SirSerow/ESP-32_Smart_Button/doc/battery_view.jpg

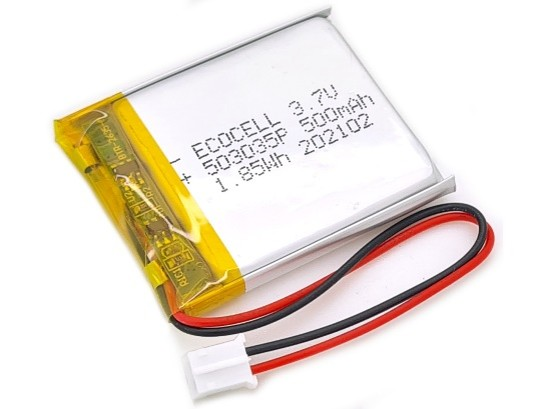
doc/battery_view.jpg
