SirSerow/ESP-32_Smart_Button/doc/cad_view.png

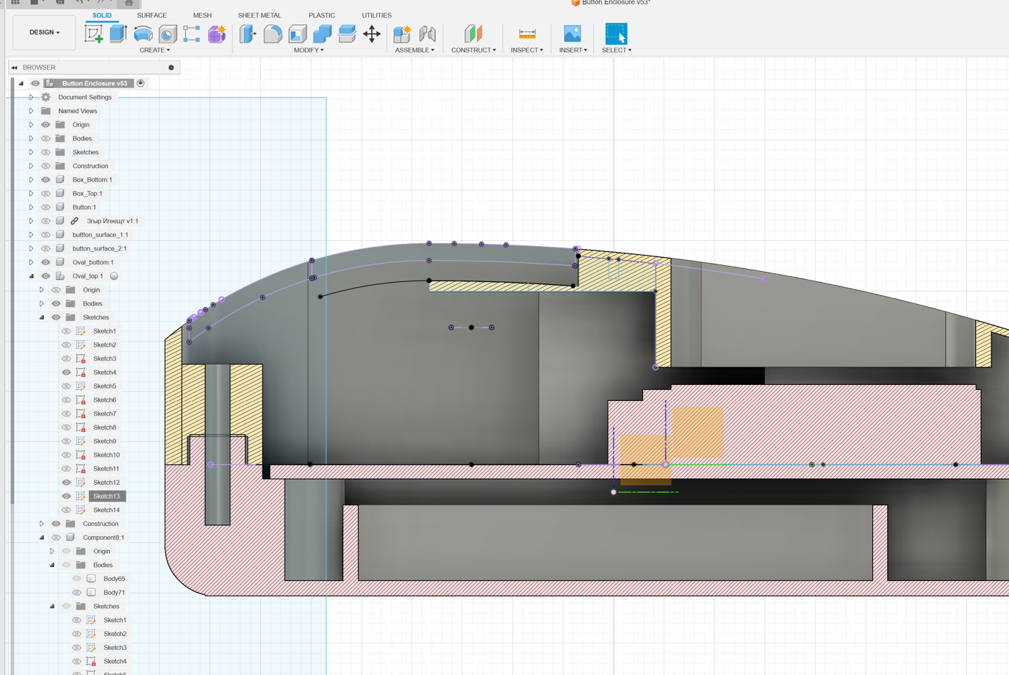
doc/cad_view.png
