SirSerow/ESP-32_Smart_Button/hardware/button-12x12-1.snapshot.1/button 12x12/button 12x12.png

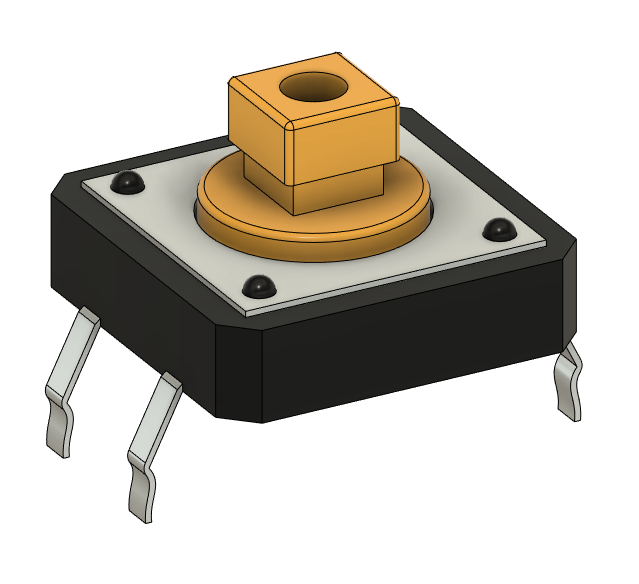
hardware/button-12x12-1.snapshot.1/button 12x12/button 12x12.png
