SirSerow/ESP-32_Smart_Button/software/magic_button/bckgrnd/contact.jpg

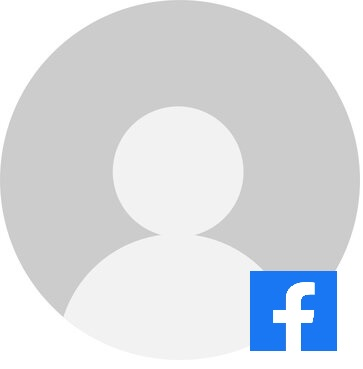
software/magic_button/bckgrnd/contact.jpg
