SirSerow/ESP-32_Smart_Button/software/magic_button/bckgrnd/FocusContact (1).webp

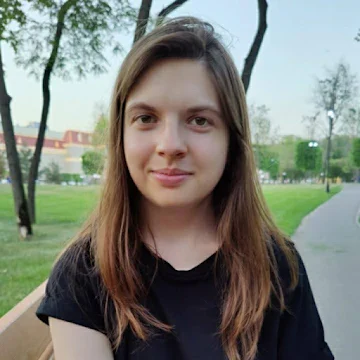
software/magic_button/bckgrnd/FocusContact (1).webp
