SirSerow/ESP-32_Smart_Button/software/magic_button/bckgrnd/FocusContact.webp

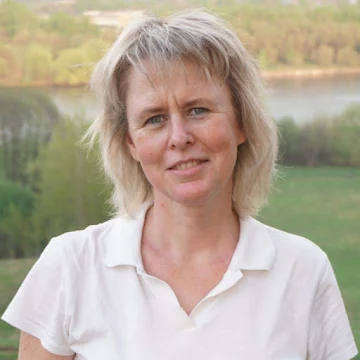
software/magic_button/bckgrnd/FocusContact.webp
