SirSerow/ESP-32_Smart_Button/software/magic_button/bckgrnd/istockphoto-1253926432-612x612.jpg

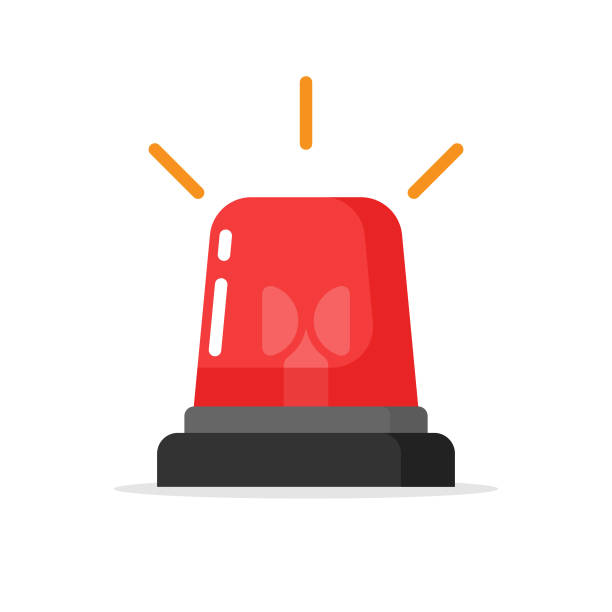
software/magic_button/bckgrnd/istockphoto-1253926432-612x612.jpg
