SirSerow/ESP-32_Smart_Button/software/magic_button/bckgrnd/pck_png/call_img.png

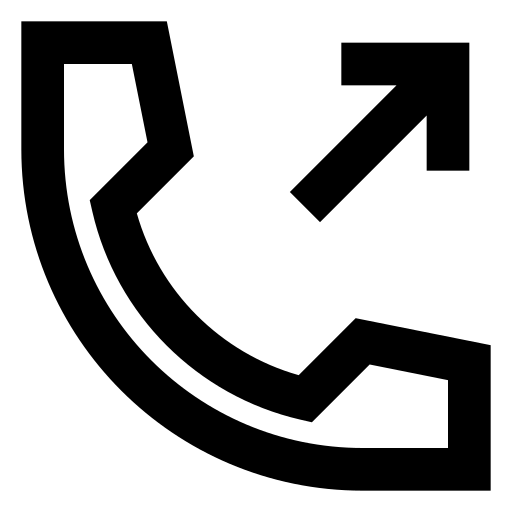
software/magic_button/bckgrnd/pck_png/call_img.png
