SirSerow/ESP-32_Smart_Button/software/magic_button/bckgrnd/pck_png/drive_flash_usb_img.png

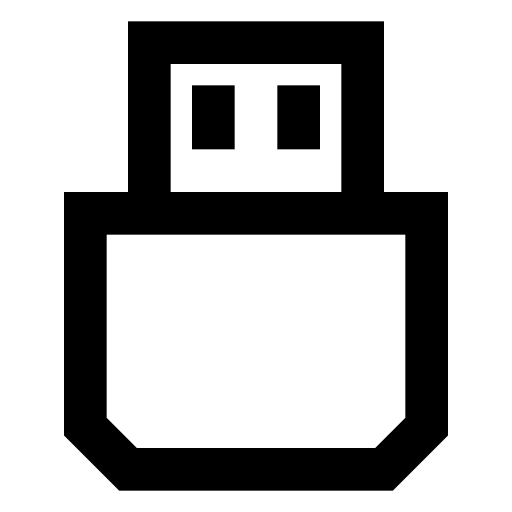
software/magic_button/bckgrnd/pck_png/drive_flash_usb_img.png
