SirSerow/ESP-32_Smart_Button/software/magic_button/bckgrnd/pck_png/square_delete_remove.png

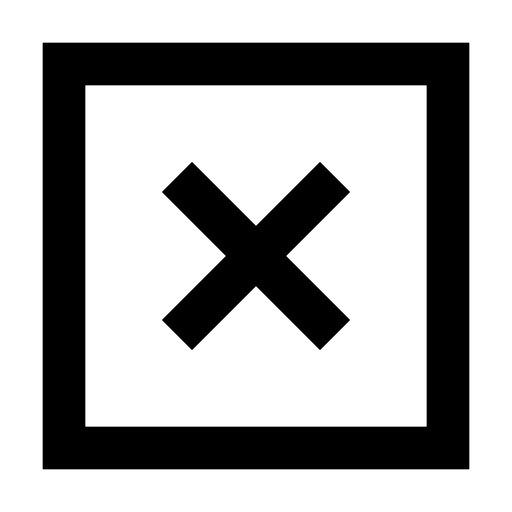
software/magic_button/bckgrnd/pck_png/square_delete_remove.png
