SirSerow/ESP-32_Smart_Button/software/magic_button/bckgrnd/wmn.jpg

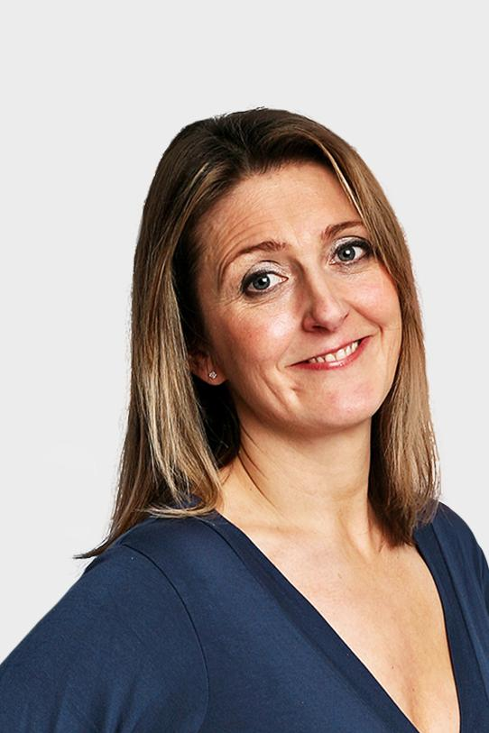
software/magic_button/bckgrnd/wmn.jpg
