SirSerow/ESP-32_Smart_Button/hardware/3d/Mouse_Button_V3.stl

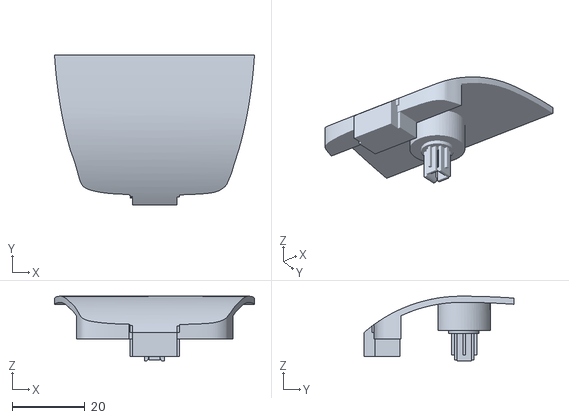
[picture p49: CAD file, 2025-02-04]
hardware/3d/Mouse_Button_V3.stl
54.9 x 41.2 x 17.7
