SirSerow/ESP-32_Smart_Button/hardware/3d/Oval_Top_V2.stl

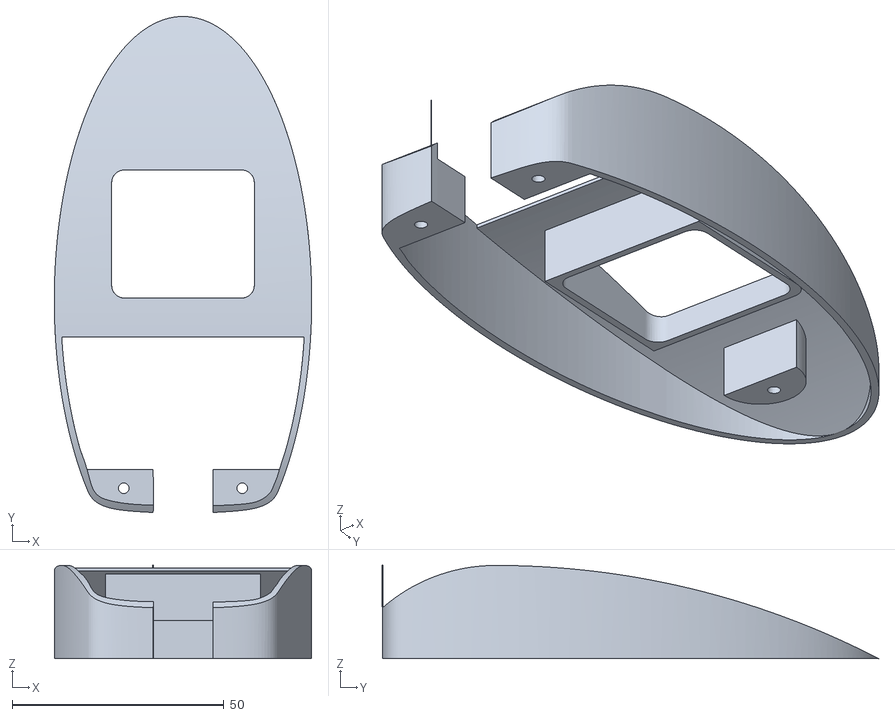
[picture p50: CAD file, 2025-02-04]
hardware/3d/Oval_Top_V2.stl
60.8 x 117.2 x 22.0
