SirSerow/ESP-32_Smart_Button/hardware/3d/Button_top_v2.stl

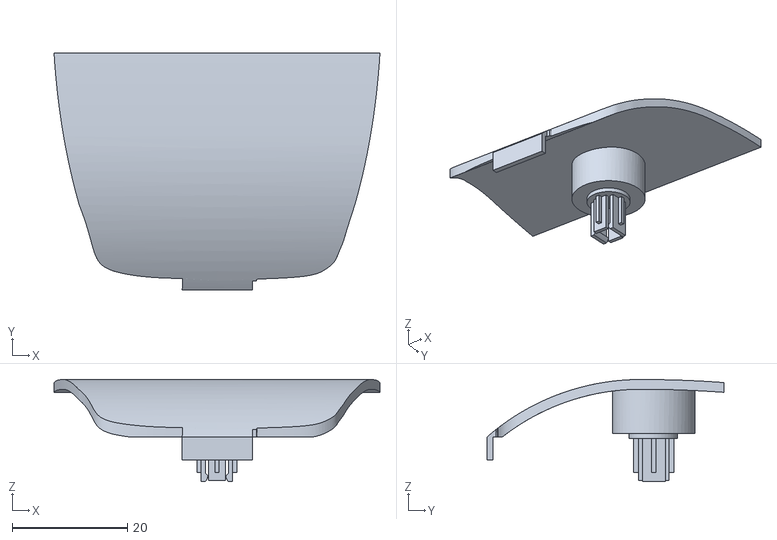
[picture p51: CAD file, 2025-02-04]
hardware/3d/Button_top_v2.stl
56.7 x 41.2 x 17.7
