SirSerow/ESP-32_Smart_Button/hardware/3d/switch_modify.stl

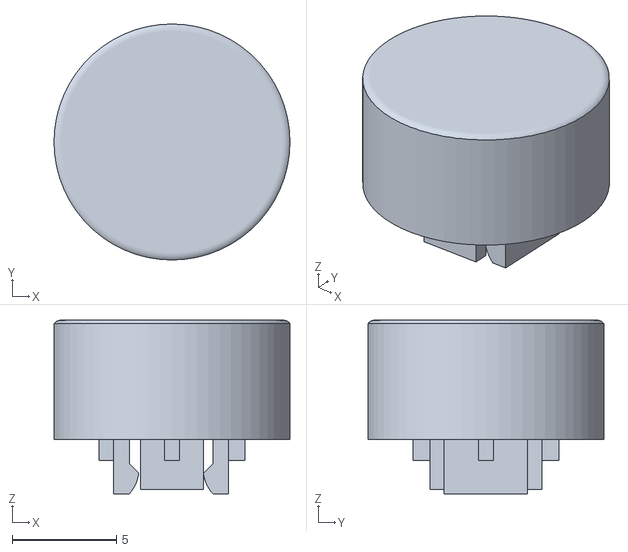
[picture p52: CAD file, 2025-02-04]
hardware/3d/switch_modify.stl
11.3 x 11.3 x 8.32
