SirSerow/ESP-32_Smart_Button/hardware/3d/Oval_Bottom_v2.stl

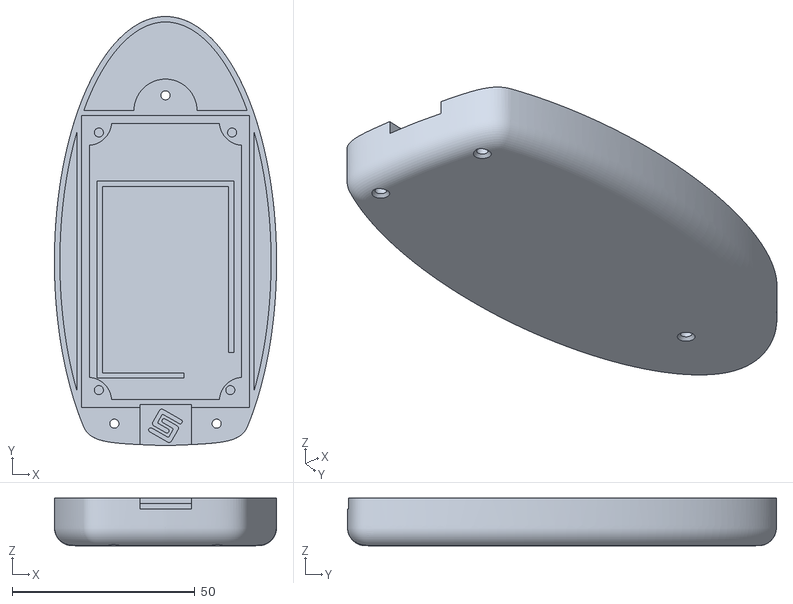
[picture p53: CAD file, 2025-02-04]
hardware/3d/Oval_Bottom_v2.stl
60.8 x 117.4 x 13.0
