SirSerow/ESP-32_Smart_Button/hardware/3d/HN1x19-PinHeader_1x19_P2.54mm_Vertical.step

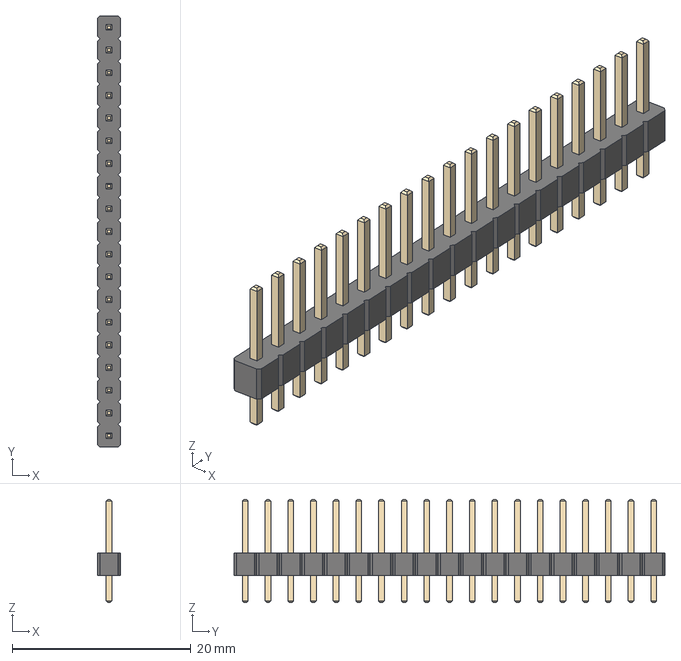
[picture p54: CAD file, 2025-02-04]
hardware/3d/HN1x19-PinHeader_1x19_P2.54mm_Vertical.step
2.54 x 48.3 x 11.5 mm
