SirSerow/ESP-32_Smart_Button/hardware/3d/SOT-23-5.step

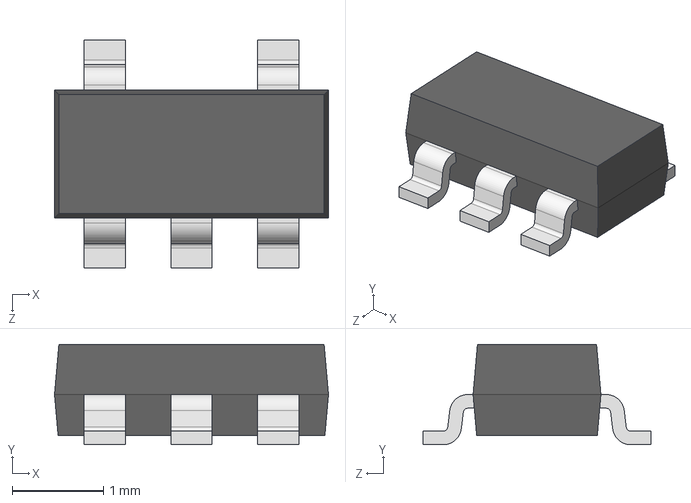
[picture p55: CAD file, 2025-02-04]
hardware/3d/SOT-23-5.step
3.00 x 1.10 x 2.50 mm
