SirSerow/ESP-32_Smart_Button/hardware/3d/BAT54.step

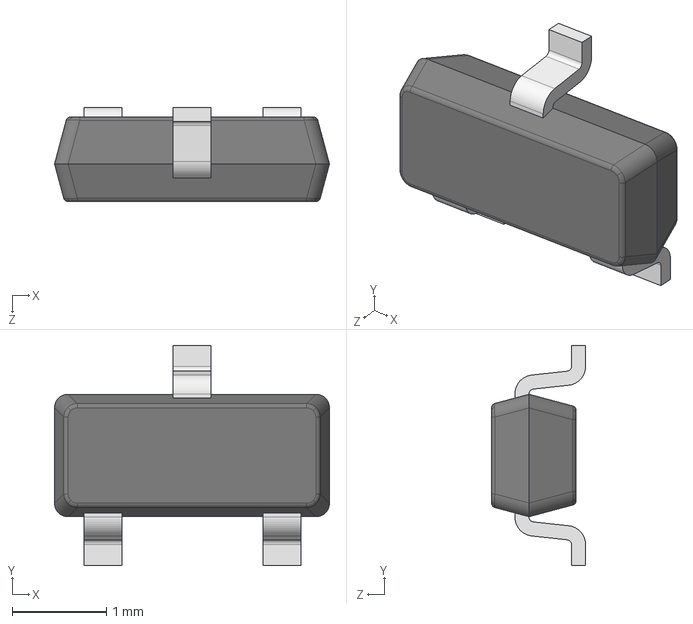
[picture p57: CAD file, 2025-02-04]
hardware/3d/BAT54.step
2.92 x 2.34 x 1.00 mm
