SirSerow/ESP-32_Smart_Button/hardware/3d/it1185.step

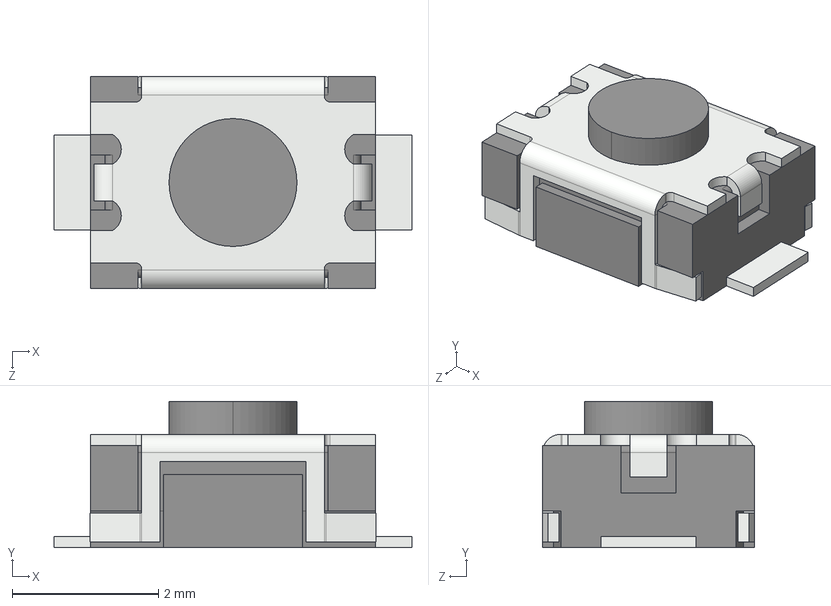
[picture p58: CAD file, 2025-02-04]
hardware/3d/it1185.step
4.90 x 2.00 x 2.90 mm
