SirSerow/ESP-32_Smart_Button/hardware/3d/ESP32-WROOM-32D-56544.STEP

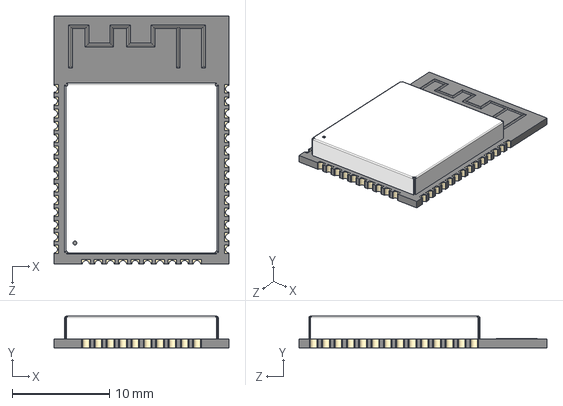
[picture p59: CAD file, 2025-02-04]
hardware/3d/ESP32-WROOM-32D-56544.STEP
18.0 x 3.25 x 25.5 mm
