SirSerow/ESP-32_Smart_Button/hardware/3d/SOD123.step

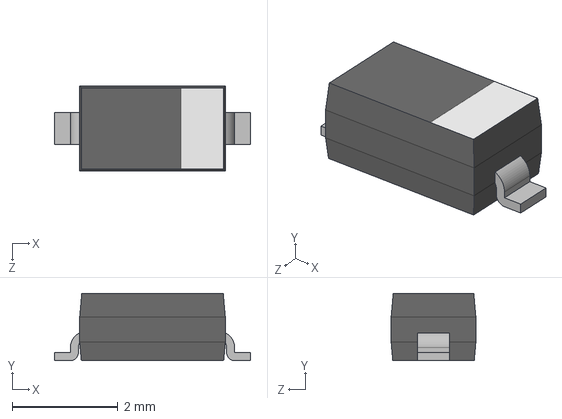
[picture p60: CAD file, 2025-02-04]
hardware/3d/SOD123.step
3.70 x 1.27 x 1.60 mm
