SirSerow/ESP-32_Smart_Button/doc/print_view.gif

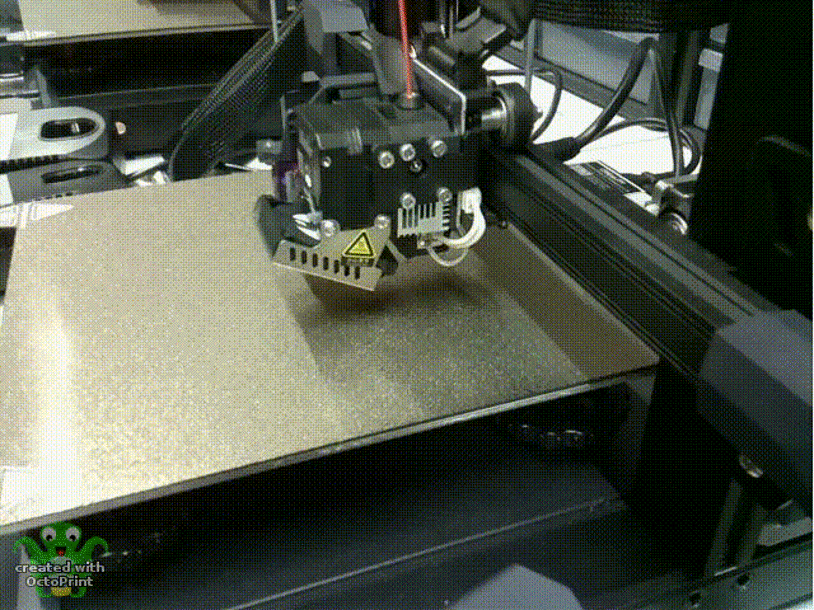
doc/print_view.gif
