SirSerow/ESP-32_Smart_Button/firmware/src/connection_lost.h

unsigned char connection_lost_pic_bmp[] = {
  0x42, 0x4d, 0x8a, 0x00, 0x01, 0x00, 0x00, 0x00, 0x00, 0x00, 0x8a, 0x00,
  0x00, 0x00, 0x7c, 0x00, 0x00, 0x00, 0x80, 0x00, 0x00, 0x00, 0x80, 0x00,
  0x00, 0x00, 0x01, 0x00, 0x20, 0x00, 0x03, 0x00, 0x00, 0x00, 0x00, 0x00,
  0x01, 0x00, 0x00, 0x00, 0x00, 0x00, 0x00, 0x00, 0x00, 0x00, 0x00, 0x00,
  0x00, 0x00, 0x00, 0x00, 0x00, 0x00, 0x00, 0x00, 0xff, 0x00, 0x00, 0xff,
  0x00, 0x00, 0xff, 0x00, 0x00, 0x00, 0x00, 0x00, 0x00, 0xff, 0x42, 0x47,
  0x52, 0x73, 0x80, 0xc2, 0xf5, 0x28, 0x60, 0xb8, 0x1e, 0x15, 0x20, 0x85,
  0xeb, 0x01, 0x40, 0x33, 0x33, 0x13, 0x80, 0x66, 0x66, 0x26, 0x40, 0x66,
  0x66, 0x06, 0xa0, 0x99, 0x99, 0x09, 0x3c, 0x0a, 0xd7, 0x03, 0x24, 0x5c,
  0x8f, 0x32, 0x00, 0x00, 0x00, 0x00, 0x00, 0x00, 0x00, 0x00, 0x00, 0x00,
  0x00, 0x00, 0x04, 0x00, 0x00, 0x00, 0x00, 0x00, 0x00, 0x00, 0x00, 0x00,
  0x00, 0x00, 0x00, 0x00, 0x00, 0x00, 0x16, 0x22, 0x59, 0xff, 0x13, 0x1d,
  0x54, 0xff, 0x15, 0x1c, 0x55, 0xff, 0x14, 0x1e, 0x5b, 0xff, 0x14, 0x1e,
  0x5e, 0xff, 0x12, 0x1c, 0x5a, 0xff, 0x12, 0x1c, 0x5b, 0xff, 0x12, 0x1c,
  0x5b, 0xff, 0x11, 0x1c, 0x58, 0xff, 0x11, 0x1b, 0x54, 0xff, 0x13, 0x1c,
  0x4e, 0xff, 0x13, 0x17, 0x2e, 0xff, 0x1d, 0x36, 0x57, 0xff, 0x21, 0x7a,
  0xcf, 0xff, 0x1a, 0x76, 0xcb, 0xff, 0x18, 0x77, 0xcf, 0xff, 0x1a, 0x74,
  0xcd, 0xff, 0x18, 0x70, 0xcc, 0xff, 0x18, 0x6d, 0xce, 0xff, 0x19, 0x6a,
  0xcc, 0xff, 0x15, 0x64, 0xd2, 0xff, 0x2b, 0x5b, 0x85, 0xff, 0x3c, 0x58,
  0x39, 0xff, 0x3d, 0x57, 0x3e, 0xff, 0x3b, 0x56, 0x3c, 0xff, 0x38, 0x4d,
  0x34, 0xff, 0x30, 0x44, 0x2b, 0xff, 0x2e, 0x3d, 0x27, 0xff, 0x31, 0x35,
  0x26, 0xff, 0x1f, 0x28, 0x1a, 0xff, 0x42, 0x46, 0x3f, 0xff, 0xbe, 0xd3,
  0xdc, 0xff, 0xaa, 0xd4, 0xe5, 0xff, 0x9d, 0xd1, 0xe4, 0xff, 0x83, 0xcb,
  0xe3, 0xff, 0x4e, 0xc0, 0xe6, 0xff, 0x37, 0x8d, 0xc9, 0xff, 0x15, 0x25,
  0x7a, 0xff, 0x13, 0x24, 0x6f, 0xff, 0x13, 0x1f, 0x66, 0xff, 0x12, 0x1f,
  0x65, 0xff, 0x12, 0x1f, 0x68, 0xff, 0x12, 0x1f, 0x6b, 0xff, 0x11, 0x20,
  0x6b, 0xff, 0x13, 0x1f, 0x6a, 0xff, 0x13, 0x1e, 0x63, 0xff, 0x14, 0x1f,
  0x64, 0xff, 0x16, 0x18, 0x38, 0xff, 0x19, 0x13, 0x0f, 0xff, 0x14, 0x10,
  0x13, 0xff, 0x43, 0x48, 0x49, 0xff, 0x99, 0xa6, 0xa6, 0xff, 0x8d, 0xa7,
  0xab, 0xff, 0x8a, 0xa6, 0xae, 0xff, 0x95, 0xa9, 0xab, 0xff, 0x9d, 0xab,
  0xa9, 0xff, 0xa2, 0xac, 0xa9, 0xff, 0xa3, 0xab, 0xa6, 0xff, 0xa6, 0xaf,
  0xaa, 0xff, 0xaa, 0xa8, 0x9f, 0xff, 0x96, 0xb5, 0xb5, 0xff, 0x75, 0xb7,
  0xc2, 0xff, 0x6c, 0xaa, 0xaf, 0xff, 0x6b, 0xa8, 0xaa, 0xff, 0x69, 0xa5,
  0xa7, 0xff, 0x71, 0xb9, 0xcb, 0xff, 0x59, 0xbb, 0xe1, 0xff, 0x40, 0xad,
  0xdc, 0xff, 0x2f, 0xa2, 0xdf, 0xff, 0x7b, 0xa1, 0xb2, 0xff, 0xbb, 0xaa,
  0x92, 0xff, 0xbd, 0xb8, 0xa9, 0xff, 0xc0, 0xd4, 0xdd, 0xff, 0xb3, 0xd0,
  0xdc, 0xff, 0x97, 0xb5, 0xd2, 0xff, 0x86, 0xa5, 0xca, 0xff, 0xb3, 0xc9,
  0xd4, 0xff, 0x55, 0x67, 0xb3, 0xff, 0x0d, 0x28, 0xb2, 0xff, 0x1b, 0x38,
  0xb6, 0xff, 0x1b, 0x3a, 0xb8, 0xff, 0x1f, 0x44, 0xb8, 0xff, 0x1e, 0x4c,
  0xb9, 0xff, 0x23, 0x58, 0xbe, 0xff, 0x23, 0x64, 0xc3, 0xff, 0x24, 0x66,
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
};
unsigned int connection_lost_pic_bmp_len = 65674;
