SirSerow/ESP-32_Smart_Button/firmware/src/my_image_1.h

unsigned char pic_in_office[] = {
  0x42, 0x4d, 0x8a, 0xfc, 0x00, 0x00, 0x00, 0x00, 0x00, 0x00, 0x8a, 0x00,
  0x00, 0x00, 0x7c, 0x00, 0x00, 0x00, 0x80, 0x00, 0x00, 0x00, 0x7e, 0x00,
  0x00, 0x00, 0x01, 0x00, 0x20, 0x00, 0x03, 0x00, 0x00, 0x00, 0x00, 0xfc,
  0x00, 0x00, 0x00, 0x00, 0x00, 0x00, 0x00, 0x00, 0x00, 0x00, 0x00, 0x00,
  0x00, 0x00, 0x00, 0x00, 0x00, 0x00, 0x00, 0x00, 0xff, 0x00, 0x00, 0xff,
  0x00, 0x00, 0xff, 0x00, 0x00, 0x00, 0x00, 0x00, 0x00, 0xff, 0x42, 0x47,
  0x52, 0x73, 0x80, 0xc2, 0xf5, 0x28, 0x60, 0xb8, 0x1e, 0x15, 0x20, 0x85,
  0xeb, 0x01, 0x40, 0x33, 0x33, 0x13, 0x80, 0x66, 0x66, 0x26, 0x40, 0x66,
  0x66, 0x06, 0xa0, 0x99, 0x99, 0x09, 0x3c, 0x0a, 0xd7, 0x03, 0x24, 0x5c,
  0x8f, 0x32, 0x00, 0x00, 0x00, 0x00, 0x00, 0x00, 0x00, 0x00, 0x00, 0x00,
  0x00, 0x00, 0x04, 0x00, 0x00, 0x00, 0x00, 0x00, 0x00, 0x00, 0x00, 0x00,
  0x00, 0x00, 0x00, 0x00, 0x00, 0x00, 0x43, 0x24, 0x1b, 0xff, 0x3e, 0x24,
  0x1a, 0xff, 0x41, 0x23, 0x1d, 0xff, 0x3e, 0x22, 0x19, 0xff, 0x42, 0x32,
  0x45, 0xff, 0x4c, 0x51, 0xc2, 0xff, 0x4b, 0x53, 0xcf, 0xff, 0x50, 0x51,
  0xcc, 0xff, 0x4f, 0x51, 0xcd, 0xff, 0x4e, 0x52, 0xcd, 0xff, 0x4f, 0x51,
  0xcd, 0xff, 0x52, 0x51, 0xcd, 0xff, 0x50, 0x51, 0xcd, 0xff, 0x50, 0x51,
  0xce, 0xff, 0x4f, 0x51, 0xce, 0xff, 0x50, 0x51, 0xce, 0xff, 0x4f, 0x51,
  0xd0, 0xff, 0x4d, 0x51, 0xd1, 0xff, 0x4f, 0x51, 0xcf, 0xff, 0x50, 0x52,
  0xcf, 0xff, 0x4f, 0x53, 0xd2, 0xff, 0x4e, 0x52, 0xd3, 0xff, 0x56, 0x59,
  0xd3, 0xff, 0x96, 0xa0, 0xda, 0xff, 0xc9, 0xd5, 0xdc, 0xff, 0xb8, 0xbf,
  0xd9, 0xff, 0x6e, 0x75, 0xda, 0xff, 0x53, 0x58, 0xe0, 0xff, 0x5f, 0x60,
  0xe1, 0xff, 0x58, 0x5c, 0xde, 0xff, 0x54, 0x52, 0xd7, 0xff, 0x52, 0x50,
  0xd7, 0xff, 0x4d, 0x50, 0xd7, 0xff, 0x4e, 0x50, 0xd5, 0xff, 0x53, 0x53,
  0xd0, 0xff, 0xa6, 0xae, 0xe1, 0xff, 0xe8, 0xf5, 0xf3, 0xff, 0xe2, 0xea,
  0xf0, 0xff, 0xdf, 0xe9, 0xf0, 0xff, 0xe2, 0xea, 0xf1, 0xff, 0xb7, 0xae,
  0xb1, 0xff, 0x68, 0x4e, 0x4d, 0xff, 0x60, 0x40, 0x2b, 0xff, 0x8d, 0x6e,
  0x3c, 0xff, 0x9f, 0x80, 0x47, 0xff, 0x97, 0x7b, 0x43, 0xff, 0x96, 0x79,
  0x45, 0xff, 0x97, 0x7a, 0x45, 0xff, 0x97, 0x79, 0x44, 0xff, 0x96, 0x7b,
  0x46, 0xff, 0x97, 0x7b, 0x46, 0xff, 0x98, 0x7c, 0x47, 0xff, 0x99, 0x7c,
  0x47, 0xff, 0x99, 0x7c, 0x48, 0xff, 0x97, 0x7c, 0x49, 0xff, 0x96, 0x7c,
  0x4a, 0xff, 0x97, 0x7c, 0x4b, 0xff, 0x97, 0x7c, 0x4b, 0xff, 0x96, 0x7b,
  0x48, 0xff, 0x98, 0x7c, 0x46, 0xff, 0x9a, 0x7c, 0x43, 0xff, 0x9a, 0x7d,
  0x44, 0xff, 0x97, 0x7c, 0x47, 0xff, 0x98, 0x7c, 0x47, 0xff, 0x97, 0x7c,
  0x47, 0xff, 0x94, 0x7a, 0x48, 0xff, 0x93, 0x79, 0x48, 0xff, 0x92, 0x77,
  0x4c, 0xff, 0x90, 0x77, 0x4c, 0xff, 0x8d, 0x75, 0x4e, 0xff, 0x8c, 0x75,
  0x4f, 0xff, 0x8b, 0x75, 0x4c, 0xff, 0x8c, 0x74, 0x4d, 0xff, 0x8c, 0x74,
  0x4d, 0xff, 0x90, 0x74, 0x4e, 0xff, 0x8c, 0x75, 0x4e, 0xff, 0x8e, 0x75,
  0x4e, 0xff, 0x8c, 0x75, 0x4e, 0xff, 0x8d, 0x75, 0x4f, 0xff, 0x8e, 0x77,
  0x4e, 0xff, 0x8f, 0x76, 0x48, 0xff, 0x57, 0x84, 0xca, 0xff, 0x3d, 0x8b,
  0xfa, 0xff, 0x44, 0x8b, 0xf1, 0xff, 0x46, 0x8e, 0xf3, 0xff, 0x47, 0x91,
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
};
unsigned int pic_in_office_len = 64650;
