SirSerow/ESP-32_Smart_Button/firmware/src/my_image_3.h

unsigned char pic_out_of_office[] = {
  0x42, 0x4d, 0x8a, 0xfe, 0x00, 0x00, 0x00, 0x00, 0x00, 0x00, 0x8a, 0x00,
  0x00, 0x00, 0x7c, 0x00, 0x00, 0x00, 0x80, 0x00, 0x00, 0x00, 0x7f, 0x00,
  0x00, 0x00, 0x01, 0x00, 0x20, 0x00, 0x03, 0x00, 0x00, 0x00, 0x00, 0xfe,
  0x00, 0x00, 0x00, 0x00, 0x00, 0x00, 0x00, 0x00, 0x00, 0x00, 0x00, 0x00,
  0x00, 0x00, 0x00, 0x00, 0x00, 0x00, 0x00, 0x00, 0xff, 0x00, 0x00, 0xff,
  0x00, 0x00, 0xff, 0x00, 0x00, 0x00, 0x00, 0x00, 0x00, 0xff, 0x42, 0x47,
  0x52, 0x73, 0x80, 0xc2, 0xf5, 0x28, 0x60, 0xb8, 0x1e, 0x15, 0x20, 0x85,
  0xeb, 0x01, 0x40, 0x33, 0x33, 0x13, 0x80, 0x66, 0x66, 0x26, 0x40, 0x66,
  0x66, 0x06, 0xa0, 0x99, 0x99, 0x09, 0x3c, 0x0a, 0xd7, 0x03, 0x24, 0x5c,
  0x8f, 0x32, 0x00, 0x00, 0x00, 0x00, 0x00, 0x00, 0x00, 0x00, 0x00, 0x00,
  0x00, 0x00, 0x04, 0x00, 0x00, 0x00, 0x00, 0x00, 0x00, 0x00, 0x00, 0x00,
  0x00, 0x00, 0x00, 0x00, 0x00, 0x00, 0x5f, 0x36, 0x3c, 0xff, 0x5a, 0x35,
  0x3c, 0xff, 0x72, 0x46, 0x43, 0xff, 0x87, 0x58, 0x45, 0xff, 0x82, 0x58,
  0x45, 0xff, 0x83, 0x58, 0x45, 0xff, 0x84, 0x56, 0x44, 0xff, 0x84, 0x56,
  0x44, 0xff, 0x84, 0x56, 0x44, 0xff, 0x84, 0x56, 0x44, 0xff, 0x84, 0x56,
  0x44, 0xff, 0x84, 0x56, 0x44, 0xff, 0x84, 0x56, 0x44, 0xff, 0x84, 0x56,
  0x44, 0xff, 0x81, 0x56, 0x43, 0xff, 0x81, 0x56, 0x43, 0xff, 0x81, 0x54,
  0x43, 0xff, 0x81, 0x55, 0x48, 0xff, 0x81, 0x53, 0x47, 0xff, 0x81, 0x54,
  0x47, 0xff, 0x80, 0x55, 0x4d, 0xff, 0x7f, 0x54, 0x4f, 0xff, 0x80, 0x55,
  0x4d, 0xff, 0x7f, 0x55, 0x4d, 0xff, 0x80, 0x55, 0x4e, 0xff, 0x81, 0x54,
  0x50, 0xff, 0x82, 0x55, 0x52, 0xff, 0x84, 0x57, 0x54, 0xff, 0x90, 0x67,
  0x5d, 0xff, 0x93, 0x6a, 0x5f, 0xff, 0x93, 0x69, 0x60, 0xff, 0x92, 0x6a,
  0x60, 0xff, 0x92, 0x6a, 0x5f, 0xff, 0x91, 0x69, 0x5e, 0xff, 0x92, 0x69,
  0x5d, 0xff, 0x93, 0x6a, 0x5e, 0xff, 0x94, 0x6a, 0x5e, 0xff, 0x94, 0x6a,
  0x5e, 0xff, 0x94, 0x6a, 0x5e, 0xff, 0x94, 0x6a, 0x5e, 0xff, 0x93, 0x69,
  0x5d, 0xff, 0x93, 0x69, 0x5d, 0xff, 0x92, 0x69, 0x5c, 0xff, 0x91, 0x68,
  0x5a, 0xff, 0x93, 0x68, 0x5c, 0xff, 0x93, 0x69, 0x5c, 0xff, 0x93, 0x6c,
  0x5c, 0xff, 0x7b, 0x50, 0x49, 0xff, 0x6a, 0x3f, 0x3f, 0xff, 0x68, 0x3f,
  0x3f, 0xff, 0x75, 0x49, 0x4a, 0xff, 0x91, 0x68, 0x60, 0xff, 0x8d, 0x65,
  0x5e, 0xff, 0x8f, 0x66, 0x5f, 0xff, 0x90, 0x66, 0x60, 0xff, 0x90, 0x66,
  0x60, 0xff, 0x8e, 0x66, 0x60, 0xff, 0x8f, 0x67, 0x61, 0xff, 0x90, 0x6a,
  0x64, 0xff, 0x90, 0x6a, 0x64, 0xff, 0x91, 0x6c, 0x66, 0xff, 0x8e, 0x69,
  0x63, 0xff, 0x8d, 0x63, 0x5e, 0xff, 0x8c, 0x62, 0x5e, 0xff, 0x8c, 0x62,
  0x5e, 0xff, 0x8a, 0x62, 0x5e, 0xff, 0x8c, 0x62, 0x5e, 0xff, 0x8c, 0x62,
  0x5f, 0xff, 0x8a, 0x62, 0x5f, 0xff, 0x8a, 0x62, 0x5f, 0xff, 0x8d, 0x61,
  0x61, 0xff, 0x8d, 0x61, 0x61, 0xff, 0x8b, 0x61, 0x60, 0xff, 0x8a, 0x61,
  0x60, 0xff, 0x89, 0x62, 0x5f, 0xff, 0x85, 0x5e, 0x5f, 0xff, 0x7b, 0x52,
  0x5f, 0xff, 0x7b, 0x52, 0x5e, 0xff, 0x7a, 0x51, 0x5d, 0xff, 0x7c, 0x50,
  0x5c, 0xff, 0x7c, 0x50, 0x5b, 0xff, 0x79, 0x50, 0x5b, 0xff, 0x71, 0x48,
  0x56, 0xff, 0x61, 0x3a, 0x4a, 0xff, 0x5d, 0x37, 0x48, 0xff, 0x60, 0x37,
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
};
unsigned int pic_out_of_office_len = 65162;
